adrian-necula/Wien_Bridge_RC_Oscillator/Simulations/bode_castig_si_faza.png

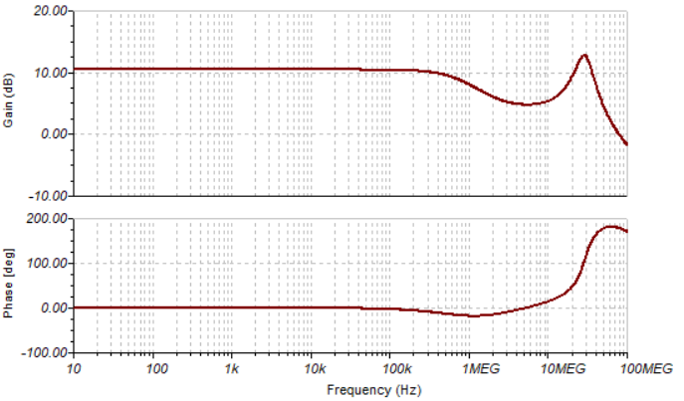
Simulations/bode_castig_si_faza.png
