adrian-necula/Wien_Bridge_RC_Oscillator/Simulations/transient_27oC_fmin.png

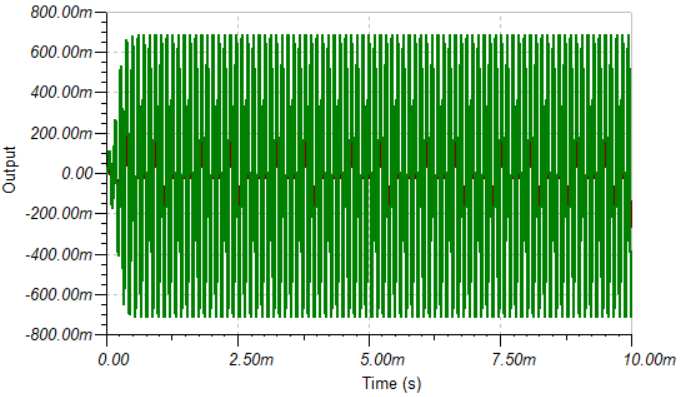
Simulations/transient_27oC_fmin.png
