adrian-necula/Wien_Bridge_RC_Oscillator/Simulations/transient_ideal.png

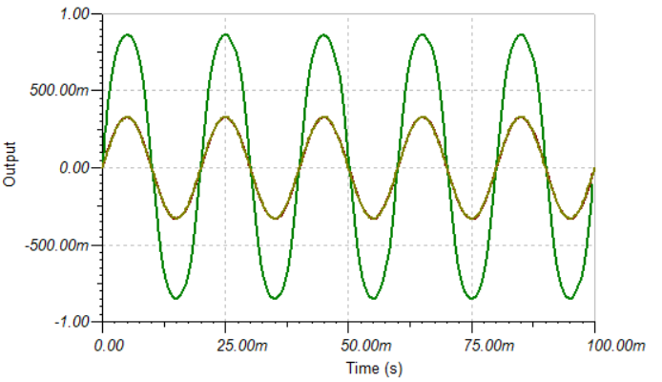
Simulations/transient_ideal.png
