adrian-necula/Wien_Bridge_RC_Oscillator/Simulations/transfer_characteristics.png

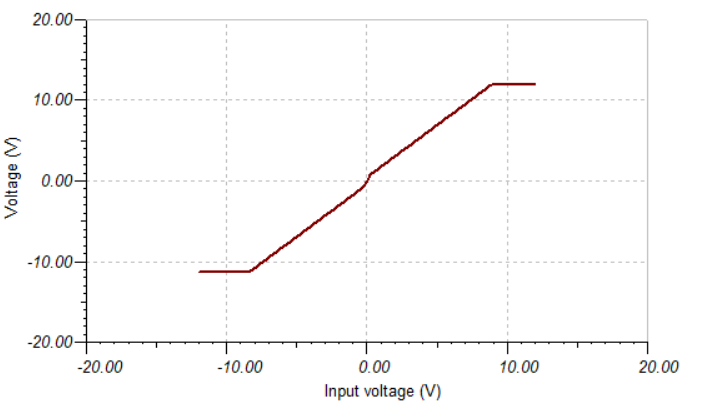
Simulations/transfer_characteristics.png
